giacu92/Arduino-Reflow-Oven-Controller/Processing-Serial-Controller/simulator/aggiornaInterfaccia.pde

void aggiornaInterfaccia()
{
  //Creo il grafico:
  int g_w = 700;
  int g_h = 500;
  PGraphics graficoProfiloSfondo = createGraphics(g_w, g_h);
  graficoProfiloSfondo.beginDraw();
    // AXIS:
    graficoProfiloSfondo.stroke(0);
    graficoProfiloSfondo.strokeWeight(3);  // Thicker
    graficoProfiloSfondo.line(startX,startY, stopX, startY); // X AXIS
    graficoProfiloSfondo.line(startX,startY, startX, stopY); // Y AXIS
    //lineette
    graficoProfiloSfondo.strokeWeight(1);
    for(int i=stepX; i<stopX-startX-10; i=i+stepX)
      graficoProfiloSfondo.line(startX+i,startY-5,startX+i,startY+5);
    for(int i=stepY; i<startY-stopY-10; i=i+stepY)
      graficoProfiloSfondo.line(startX-5,startY-i,startX+5,startY-i);
  
    //Plotto le linee del grafico di sfondo in base alle temperature stabilite
    graficoProfiloSfondo.stroke(150);
    int TEMP_SOAK_MIN_PL   = startY - round(map(TEMPERATURE_SOAK_MIN,   0, 50, 0, stepY));
    int TEMP_SOAK_MAX_PL   = startY - round(map(TEMPERATURE_SOAK_MAX,   0, 50, 0, stepY));
    int TEMP_REFLOW_MAX_PL = startY - round(map(TEMPERATURE_REFLOW_MAX, 0, 50, 0, stepY));
    int TEMP_COOL_PL       = startY - round(map(TEMPERATURE_COOLDOWN,   0, 50, 0, stepY));
    
    graficoProfiloSfondo.line(startX,startY,stepX*2.5+startX,TEMP_SOAK_MIN_PL);
    graficoProfiloSfondo.line(stepX*2.5+startX, TEMP_SOAK_MIN_PL, stepX*6+startX, TEMP_SOAK_MAX_PL);
    graficoProfiloSfondo.line(stepX*6+startX, TEMP_SOAK_MAX_PL, stepX*8+startX, TEMP_REFLOW_MAX_PL);
    graficoProfiloSfondo.line(stepX*8+startX, TEMP_REFLOW_MAX_PL, stepX*10+startX, TEMP_SOAK_MAX_PL);
    graficoProfiloSfondo.line(stepX*10+startX, TEMP_SOAK_MAX_PL, stepX*12+startX, TEMP_COOL_PL);
    
    int line_ph_x         = round(map(Integer.valueOf(DURATION_PH), 0, 30, 0, stepX));
    int line_soak_x       = round(map(Integer.valueOf(DURATION_SOAK), 0, 30, 0, stepX));
    int line_refl_peak_x  = round(map(Integer.valueOf(DURATION_REFLOW_RAMPUP), 0, 30, 0, stepX));
    
    //Plotto le linee di divisione tra le varie aree di reflow
    graficoProfiloSfondo.stroke(180);
    /* OLD
    graficoProfiloSfondo.line(startX+stepX*2.5,stopY+30,startX+stepX*2.5,startY);
    graficoProfiloSfondo.line(startX+stepX*6,stopY+30,startX+stepX*6,startY);
    graficoProfiloSfondo.line(startX+stepX*10,stopY+30,startX+stepX*10,startY);
    */
    
    graficoProfiloSfondo.line(startX+line_ph_x,             stopY+30,startX+line_ph_x            , startY);
    graficoProfiloSfondo.line(startX+line_ph_x+line_soak_x, stopY+30,startX+line_ph_x+line_soak_x, startY);
    graficoProfiloSfondo.line(startX+stepX*10,stopY+30,startX+stepX*10,startY);
    
    //Scrivo i nomi delle aree:
    graficoProfiloSfondo.stroke(0);
    graficoProfiloSfondo.fill(0, 30, 225);
    graficoProfiloSfondo.textSize(16);
    graficoProfiloSfondo.text("Preheat",  startX+40 , 70);
    graficoProfiloSfondo.text("Soak",     startX+200, 70);
    graficoProfiloSfondo.text("Reflow",   startX+390, 70);
    graficoProfiloSfondo.text("Cooldown", startX+550, 70);
    
    //creo l'insieme di punti che mi dà il grafico
    graficoProfiloSfondo.stroke(0);
    graficoProfiloSfondo.strokeWeight(2);
    for(int i=0; i<table.getRowCount(); i++)
    {
      TableRow row = table.getRow(i);
      X = row.getInt("time");
      Y = (int)row.getFloat("temperature");
      
      line(oldX, oldY, X, Y);
      oldX = X;
      oldY = Y;
    }
    if(table.getRowCount() > 0)
    {
      TableRow first_row = table.getRow(0);
      oldX = first_row.getInt("time");
      oldY = (int)first_row.getFloat("temperature");
    }
    
  graficoProfiloSfondo.endDraw();
  image(graficoProfiloSfondo, 10, 0);
}
